kalinchuk/kenbak_1/Original PCB/DSC_6037.jpg

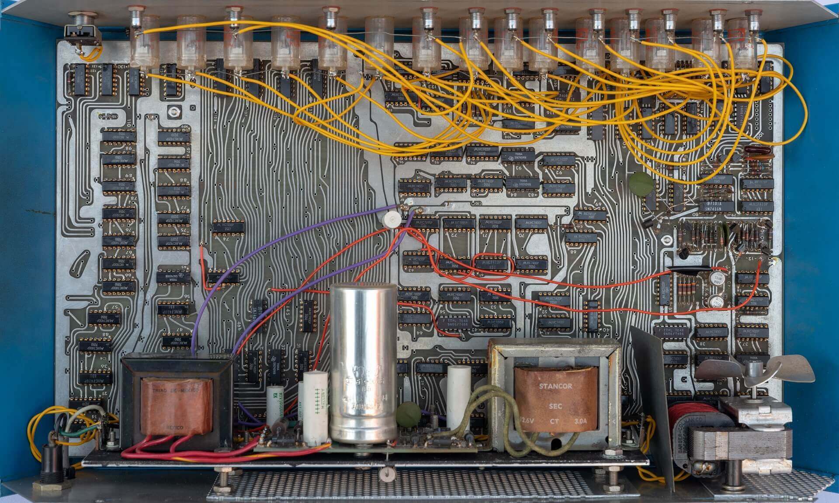
Original PCB/DSC_6037.jpg
