kalinchuk/kenbak_1/Original PCB/DSC_6046.jpg

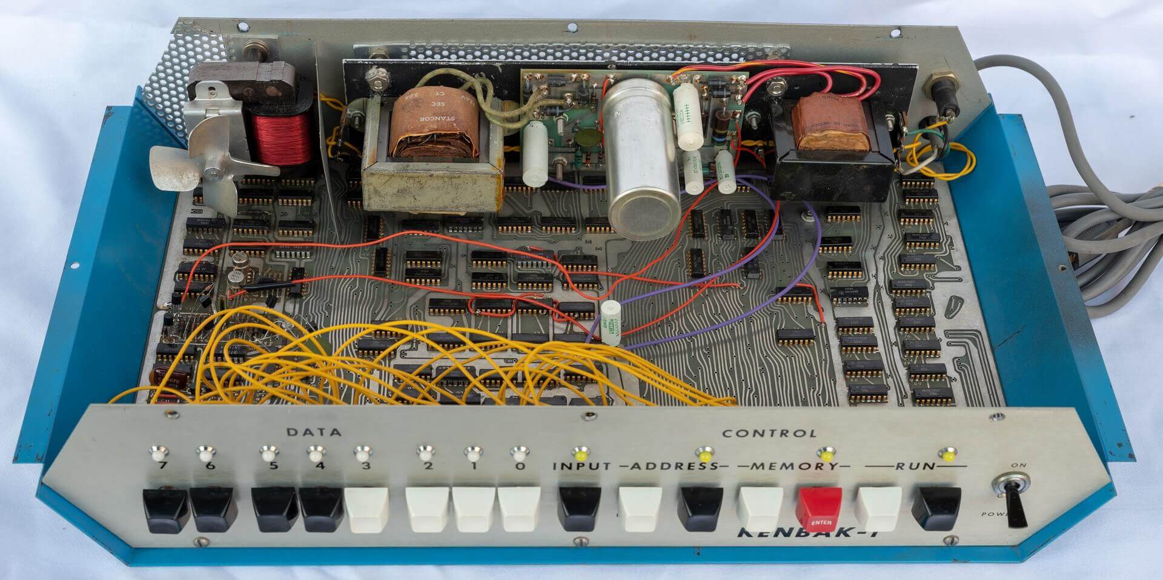
Original PCB/DSC_6046.jpg
