kalinchuk/kenbak_1/Original PCB/DSC_6112.jpg

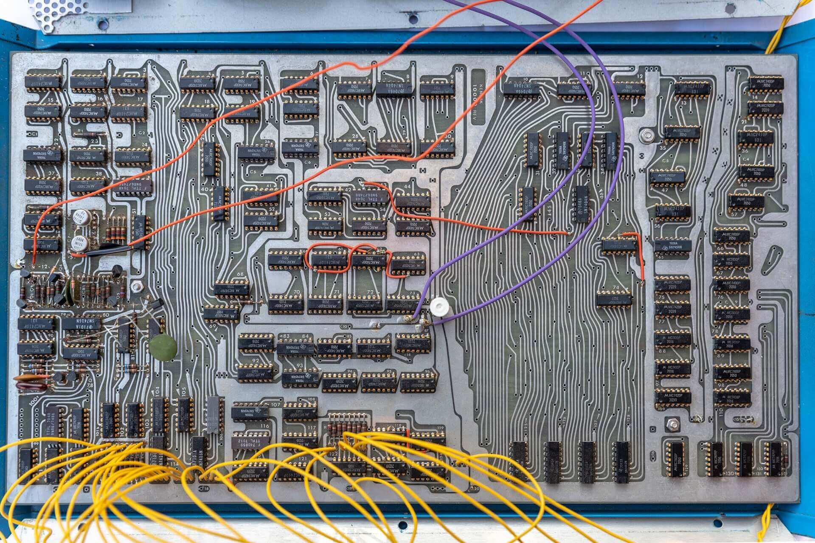
Original PCB/DSC_6112.jpg
