kalinchuk/kenbak_1/Original Power Supply/20220929_121505.jpg

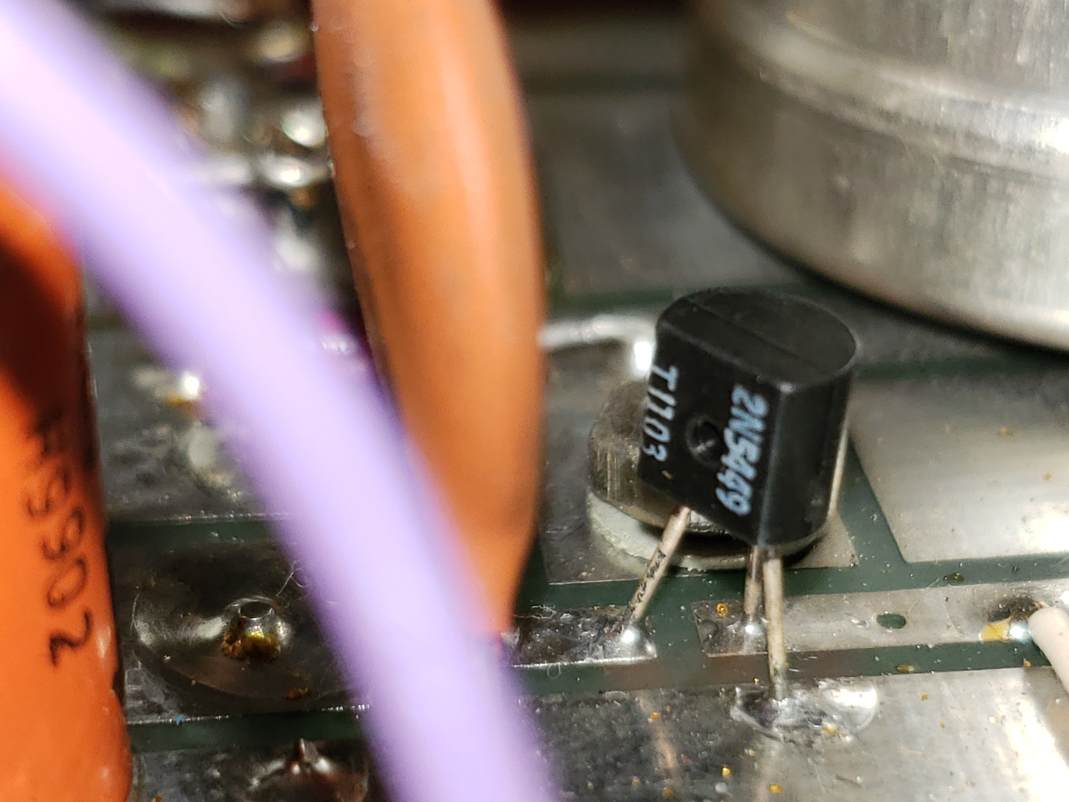
Original Power Supply/20220929_121505.jpg
