kalinchuk/kenbak_1/Original Power Supply/20220929_124913.jpg

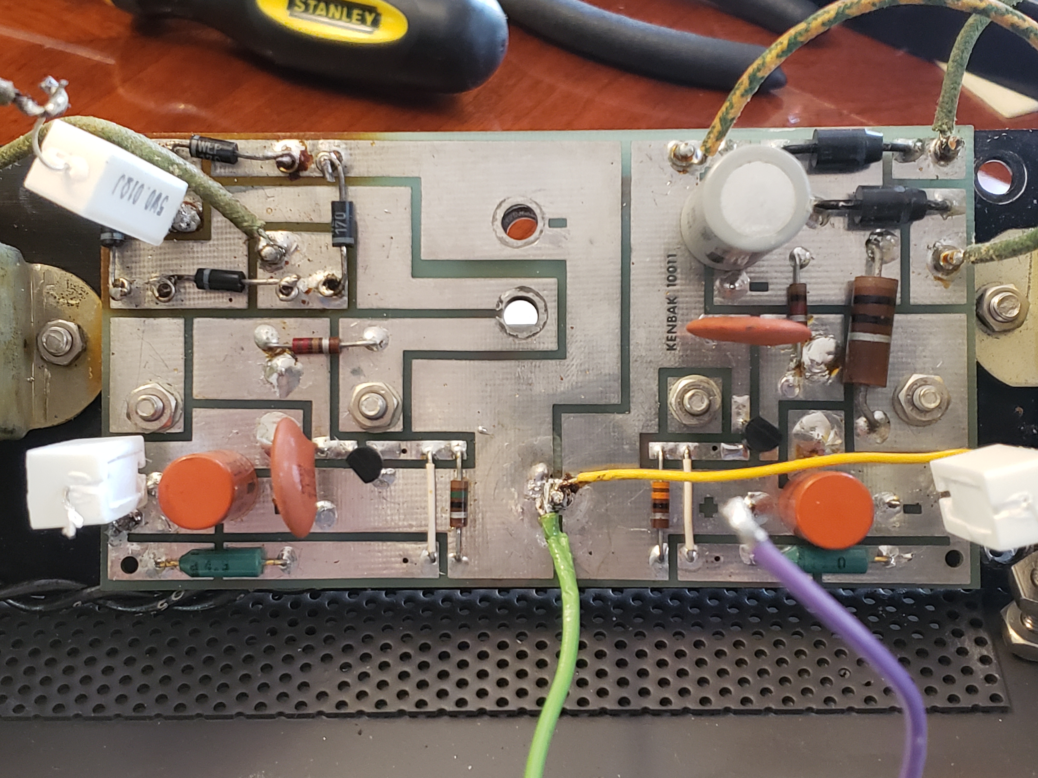
Original Power Supply/20220929_124913.jpg
