kalinchuk/kenbak_1/Original Power Supply/20220929_130458.jpg

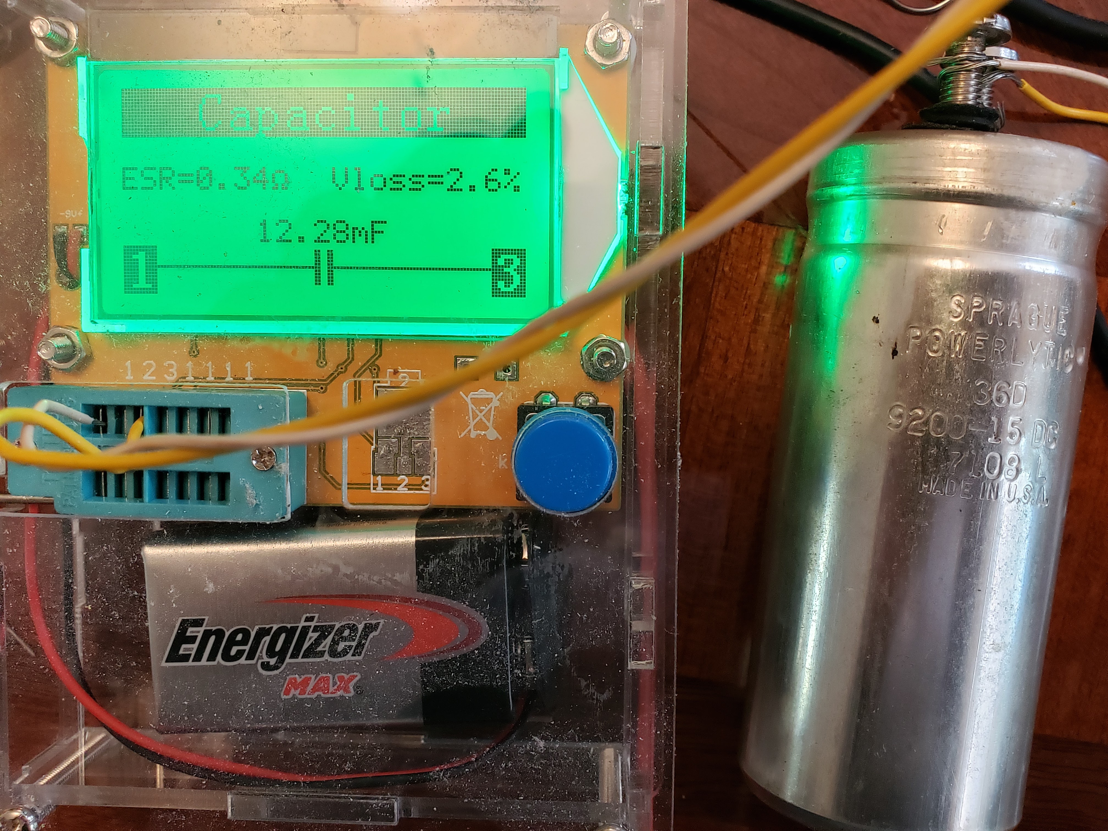
Original Power Supply/20220929_130458.jpg
