kalinchuk/kenbak_1/Original Power Supply/powersupply1.jpeg

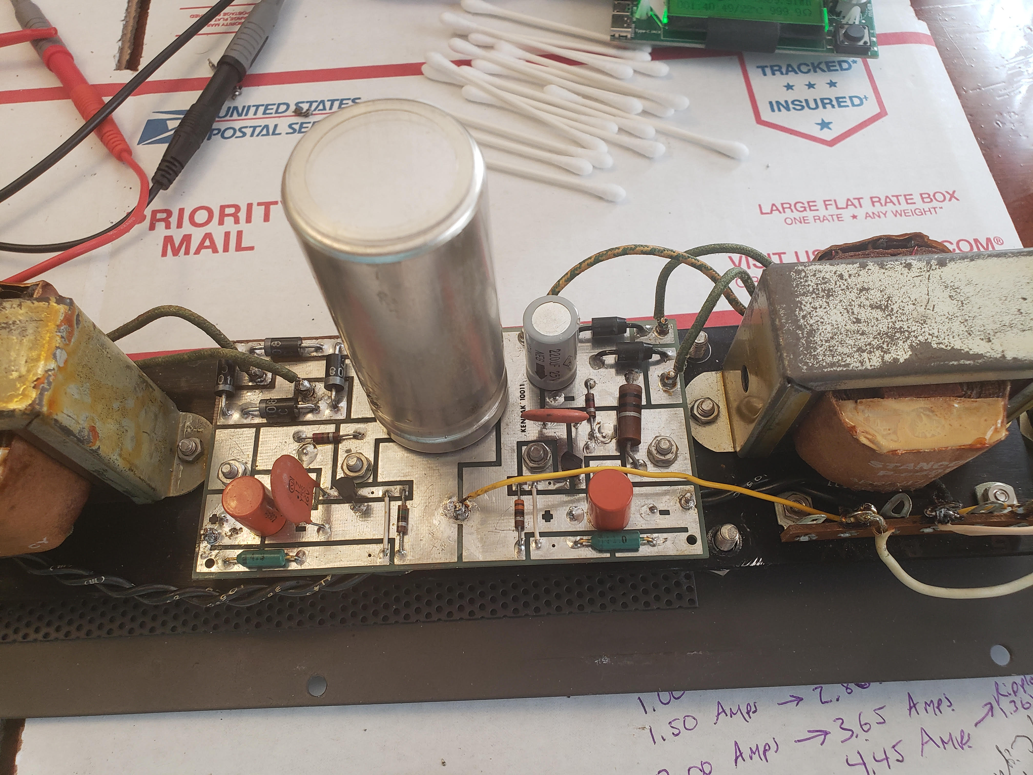
Original Power Supply/powersupply1.jpeg
