kalinchuk/kenbak_1/Original Power Supply/powersupply3.jpeg

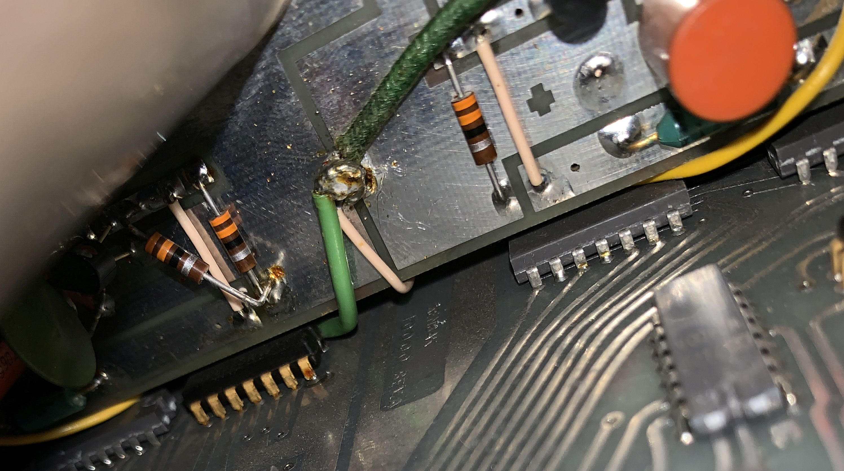
Original Power Supply/powersupply3.jpeg
