kalinchuk/kenbak_1/Original Power Supply/PowerSupply.jpg

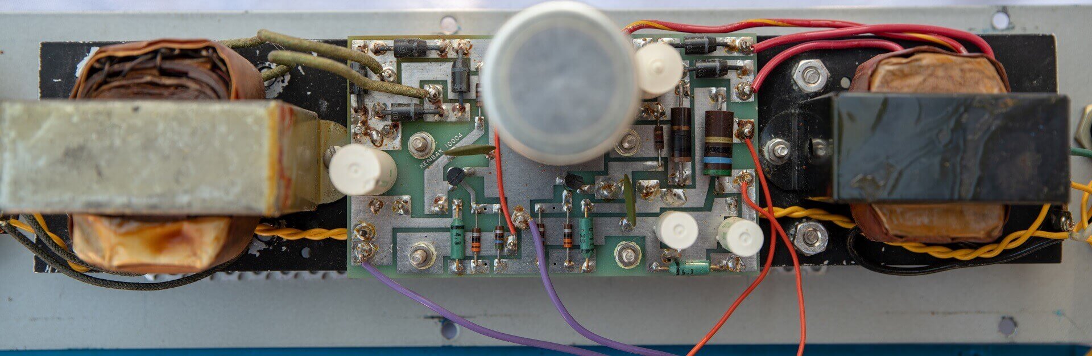
Original Power Supply/PowerSupply.jpg
