kalinchuk/kenbak_1/Original Power Supply/20220929_121420.jpg

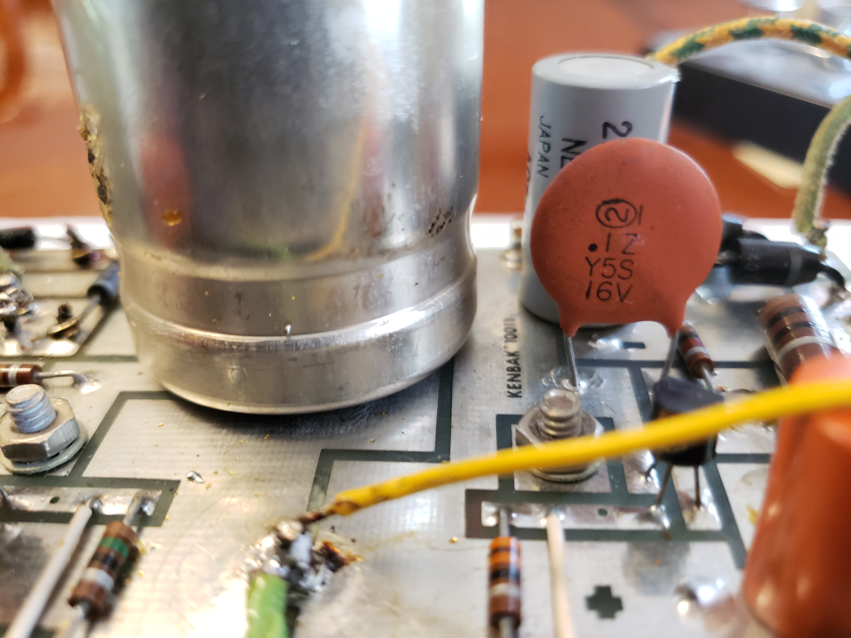
Original Power Supply/20220929_121420.jpg
