kalinchuk/kenbak_1/Original Power Supply/20220929_151645.jpg

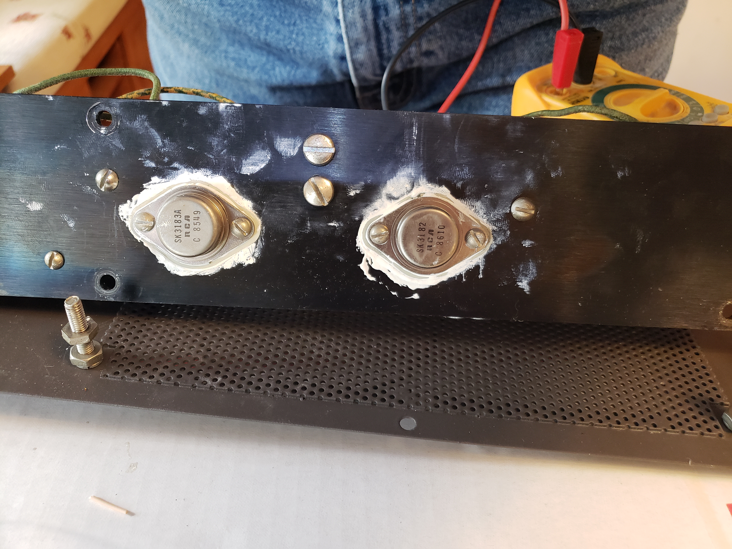
Original Power Supply/20220929_151645.jpg
